yosiaLukumai/FSO/CAD/lasers and laser ho;der assembly.SLDASM

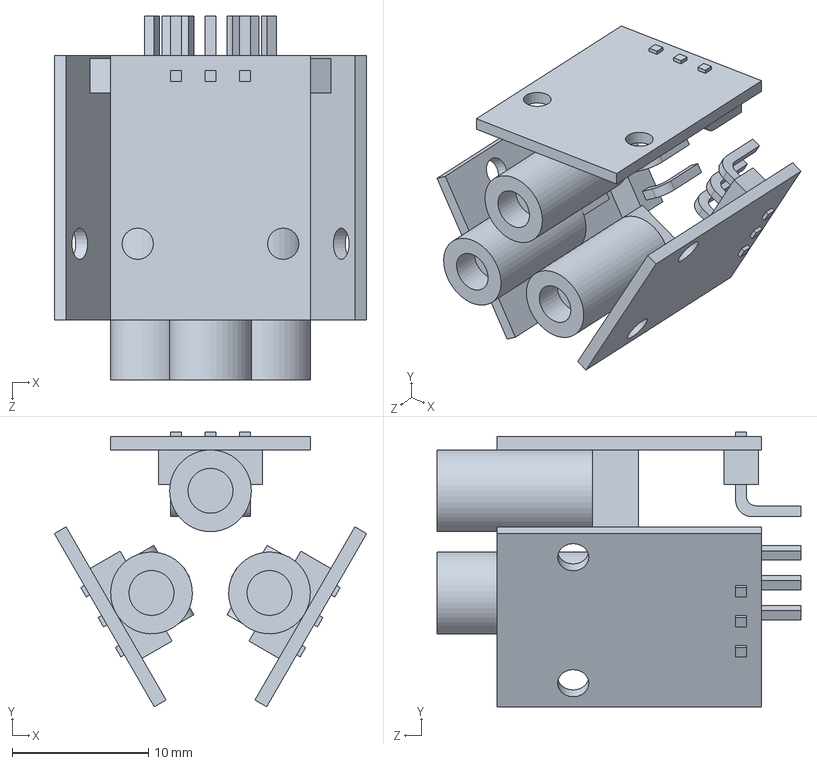
[picture p13: CAD file, 2026-05-01]
CAD/lasers and laser ho;der assembly.SLDASM
22.9 x 20.2 x 26.7 mm
LaserModule x 3
