yosiaLukumai/FSO/CAD/component holder and adjuster.SLDASM

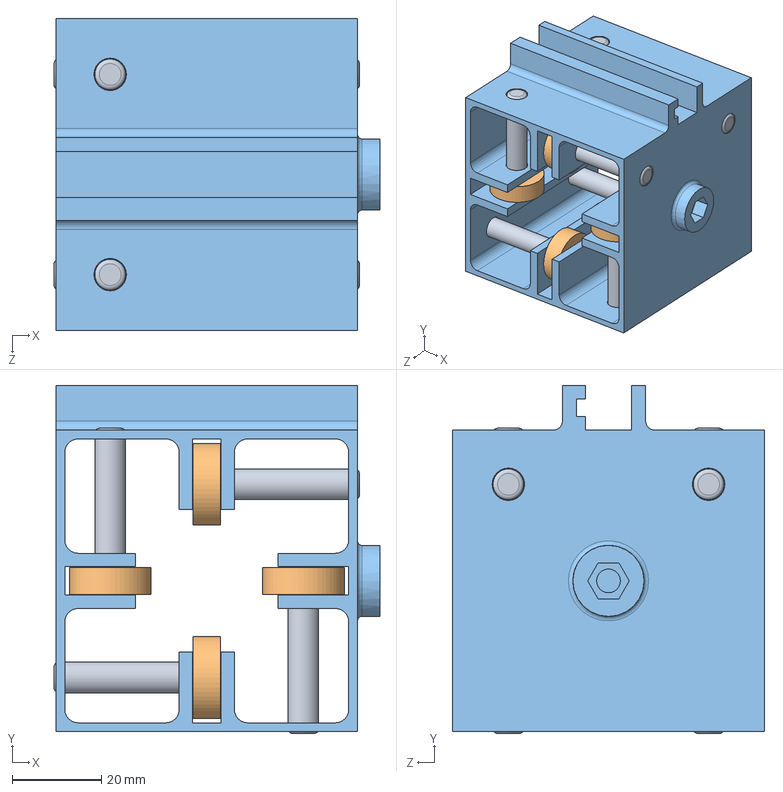
[picture p15: CAD file, 2026-05-01]
CAD/component holder and adjuster.SLDASM
73.2 x 78.2 x 70.0 mm
lens_holder
bearing x 8
bearing_holding_rods x 8
