yosiaLukumai/FSO/CAD/square-pipes-1.snapshot.1/rotation-joint-link.SLDPRT

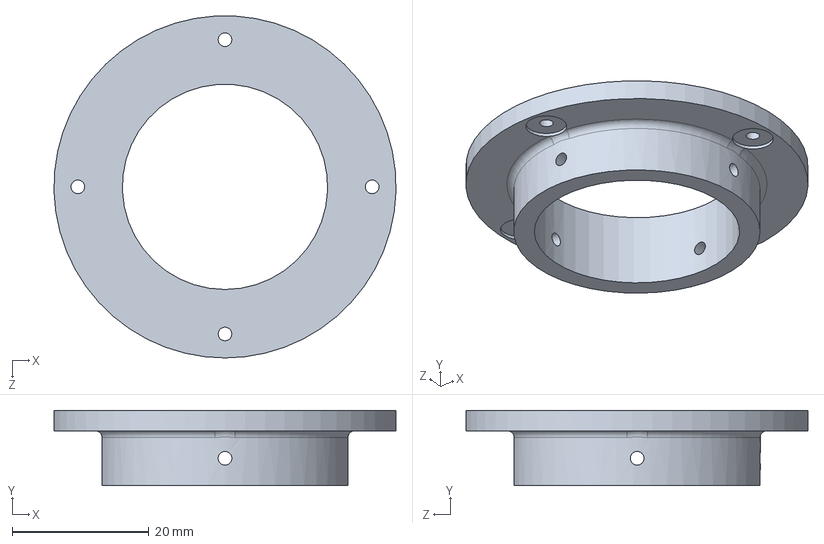
[picture p29: CAD file, 2026-05-01]
CAD/square-pipes-1.snapshot.1/rotation-joint-link.SLDPRT
50.0 x 11.0 x 50.0 mm
