yosiaLukumai/FSO/CAD/adster_concept.SLDPRT

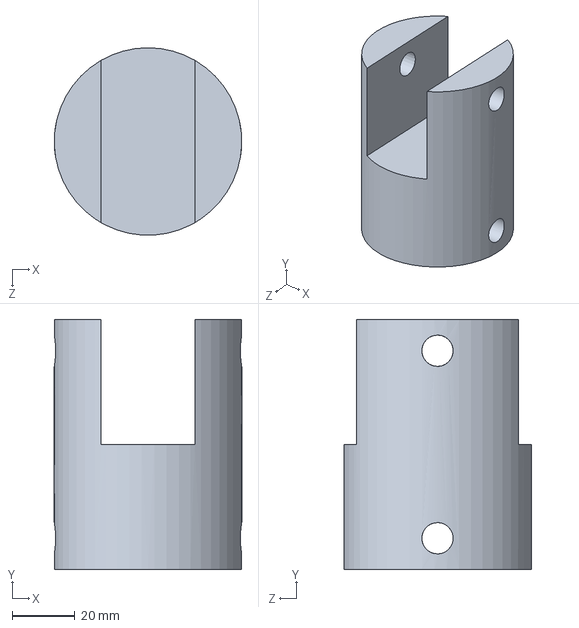
[picture p30: CAD file, 2026-05-01]
CAD/adster_concept.SLDPRT
60.0 x 80.0 x 60.0 mm
