yosiaLukumai/FSO/CAD/square-pipes-1.snapshot.1/rotational joint lock guider.SLDPRT

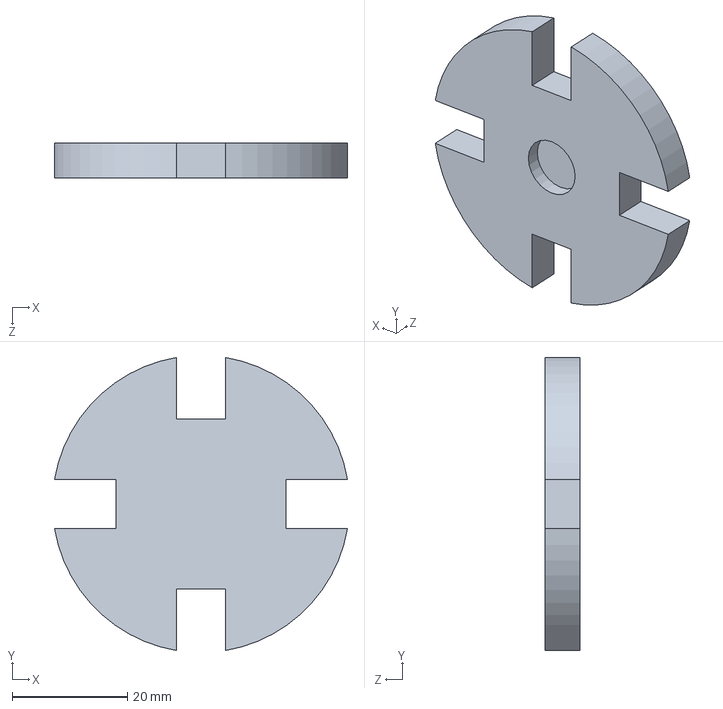
[picture p31: CAD file, 2026-05-01]
CAD/square-pipes-1.snapshot.1/rotational joint lock guider.SLDPRT
50.8 x 50.8 x 6.00 mm
