yosiaLukumai/FSO/CAD/convex22_V2.0.SLDPRT

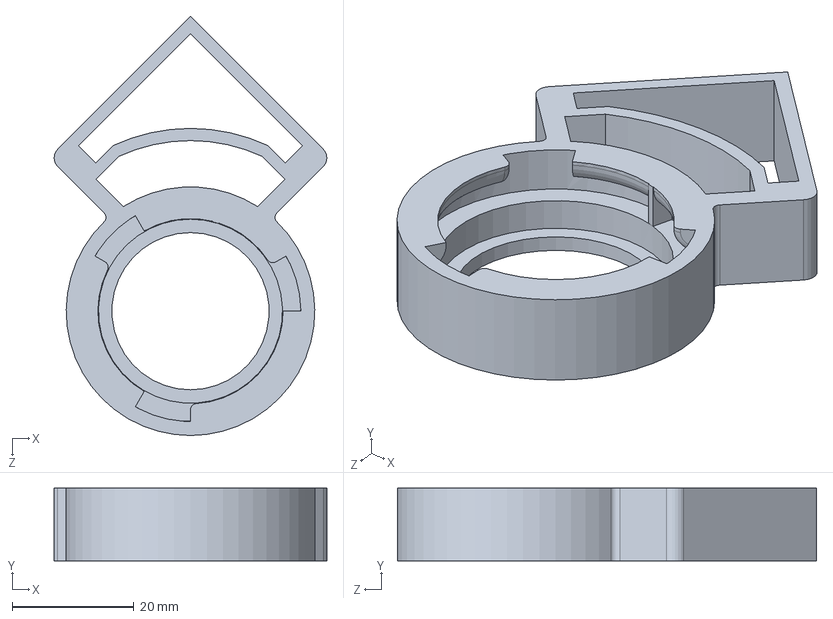
[picture p32: CAD file, 2026-05-01]
CAD/convex22_V2.0.SLDPRT
44.8 x 11.9 x 68.8 mm
