yosiaLukumai/FSO/CAD/square-pipes-1.snapshot.1/pitch lock modified.SLDPRT

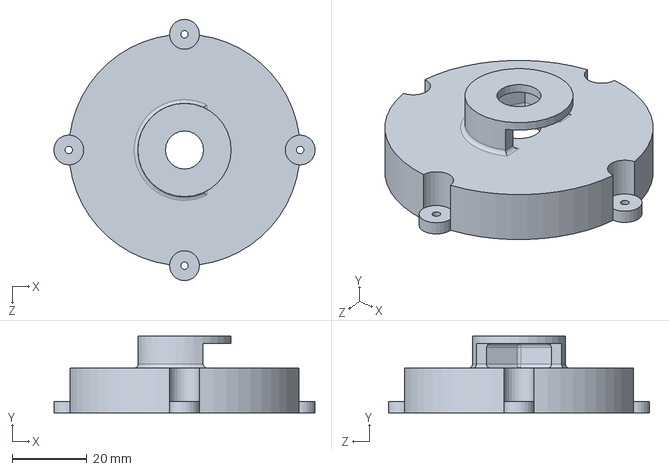
[picture p33: CAD file, 2026-05-01]
CAD/square-pipes-1.snapshot.1/pitch lock modified.SLDPRT
69.9 x 20.5 x 69.9 mm
