yosiaLukumai/FSO/CAD/bearing.SLDPRT

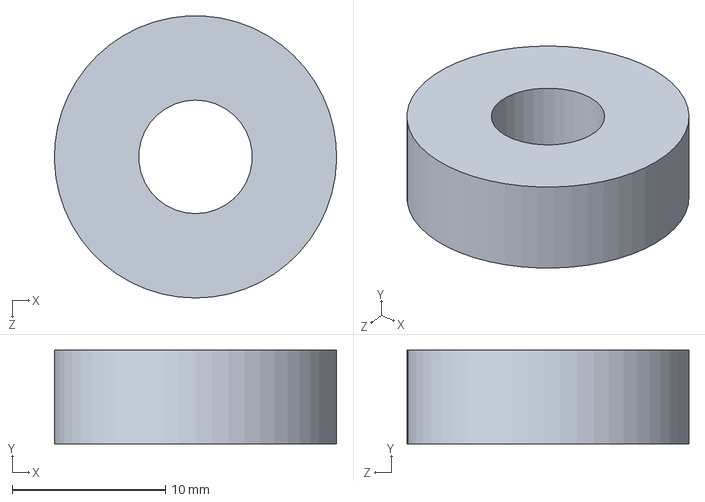
[picture p34: CAD file, 2026-05-01]
CAD/bearing.SLDPRT
18.4 x 6.10 x 18.4 mm
