yosiaLukumai/FSO/CAD/rotatonal joint external lock.SLDPRT

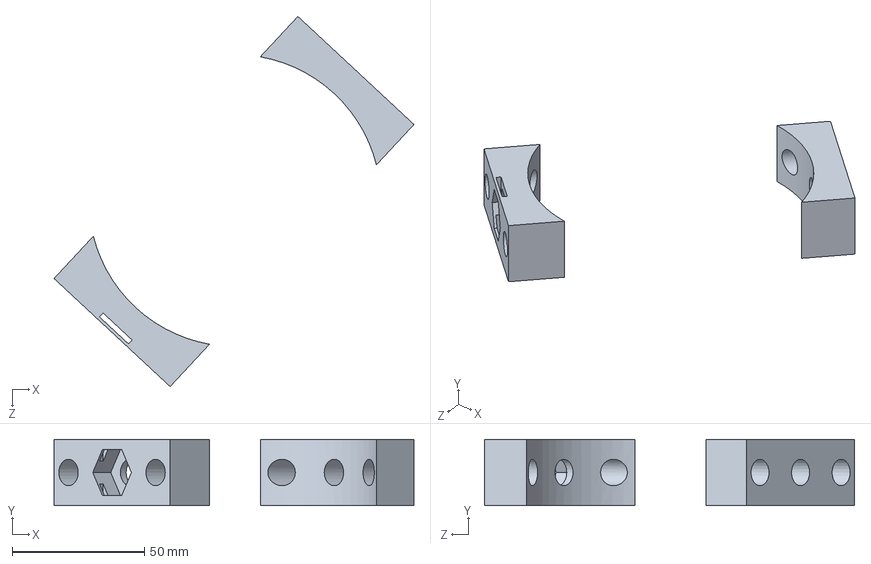
[picture p35: CAD file, 2026-05-01]
CAD/rotatonal joint external lock.SLDPRT
136.2 x 25.0 x 140.0 mm
