yosiaLukumai/FSO/CAD/square-pipes-1.snapshot.1/Slot guider.SLDPRT

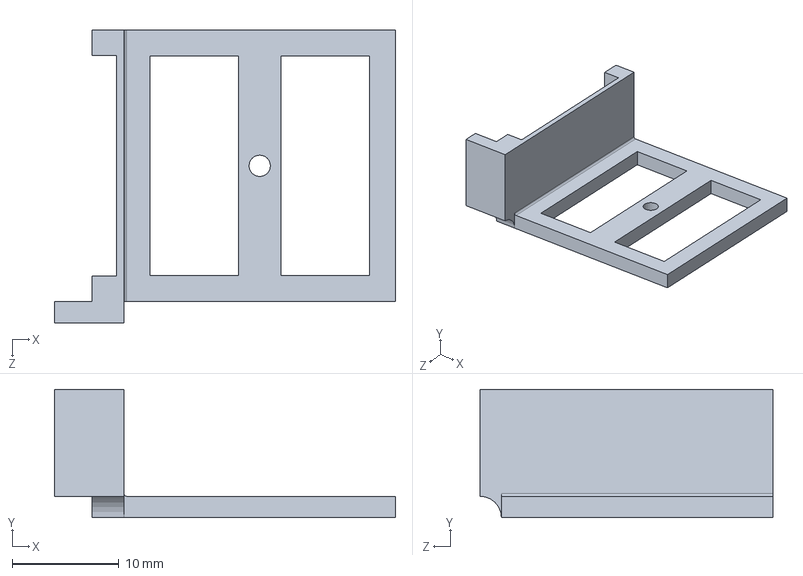
[picture p36: CAD file, 2026-05-01]
CAD/square-pipes-1.snapshot.1/Slot guider.SLDPRT
31.9 x 12.0 x 27.4 mm
