yosiaLukumai/FSO/CAD/square-pipes-1.snapshot.1/single receiver holder.SLDPRT

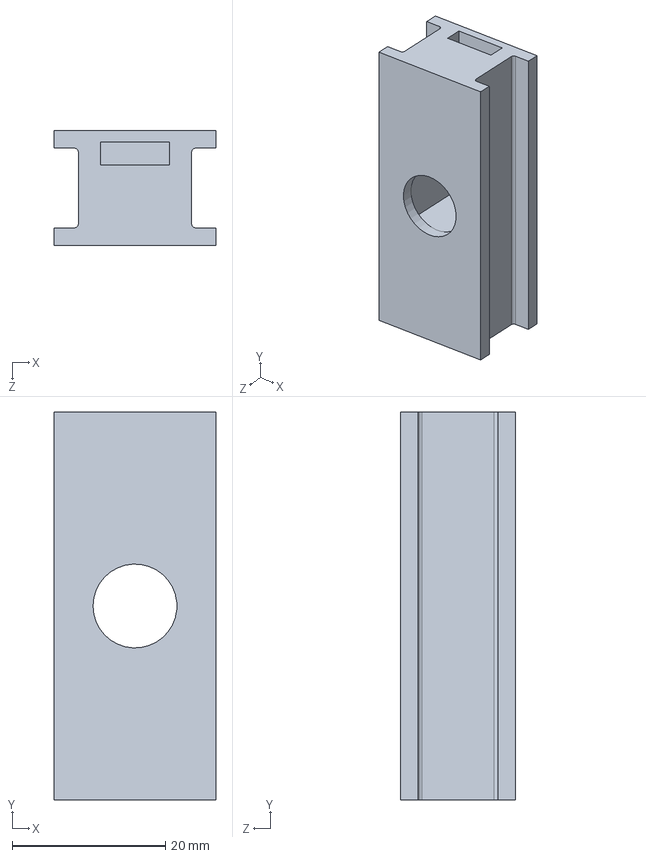
[picture p37: CAD file, 2026-05-01]
CAD/square-pipes-1.snapshot.1/single receiver holder.SLDPRT
21.1 x 50.7 x 15.0 mm
