yosiaLukumai/FSO/CAD/LaserModule.SLDPRT

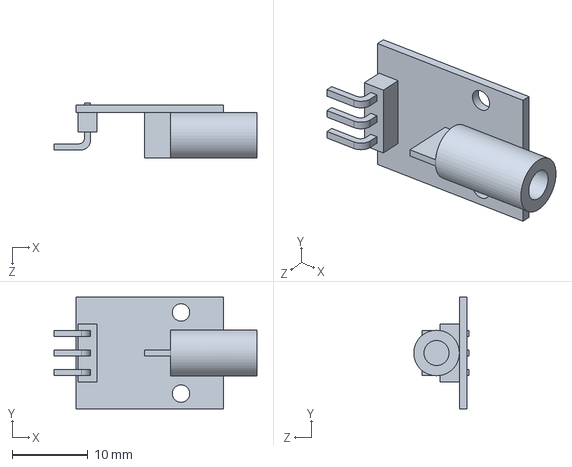
[picture p38: CAD file, 2026-05-01]
CAD/LaserModule.SLDPRT
26.7 x 14.7 x 7.30 mm
