yosiaLukumai/FSO/CAD/square-pipes-1.snapshot.1/side locks.SLDPRT

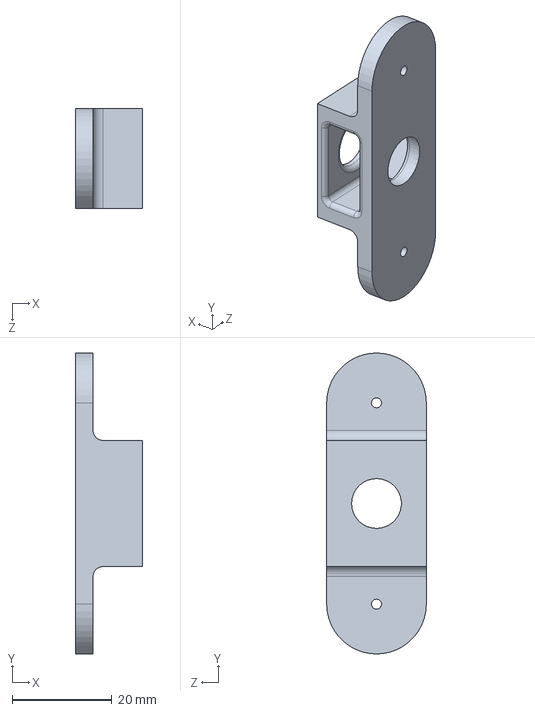
[picture p39: CAD file, 2026-05-01]
CAD/square-pipes-1.snapshot.1/side locks.SLDPRT
13.4 x 60.4 x 20.0 mm
