yosiaLukumai/FSO/CAD/square-pipes-1.snapshot.1/bearing_holding_rods.SLDPRT

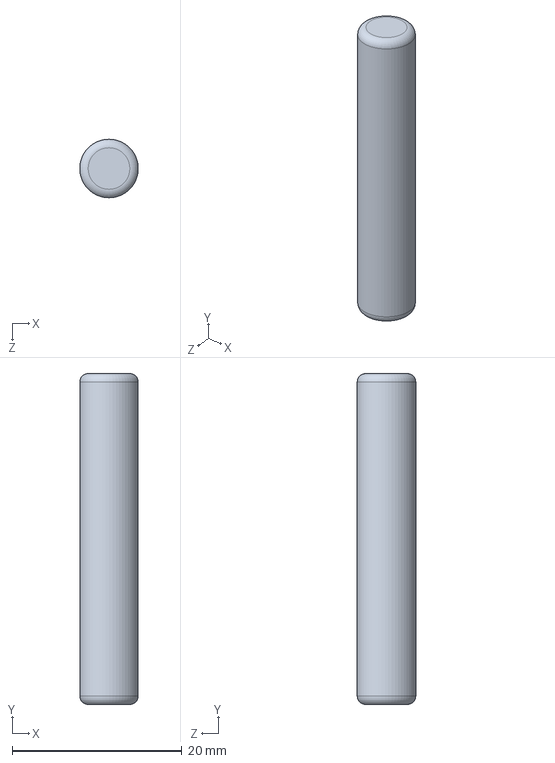
[picture p40: CAD file, 2026-05-01]
CAD/square-pipes-1.snapshot.1/bearing_holding_rods.SLDPRT
6.89 x 39.0 x 6.90 mm
