yosiaLukumai/FSO/CAD/square-pipes-1.snapshot.1/enclosure.SLDPRT

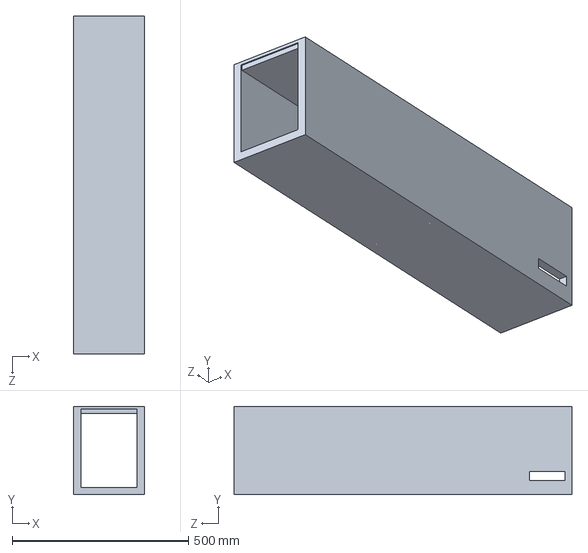
[picture p41: CAD file, 2026-05-01]
CAD/square-pipes-1.snapshot.1/enclosure.SLDPRT
200.4 x 250.0 x 960.0 mm
