yosiaLukumai/FSO/CAD/square-pipes-1.snapshot.1/standing pole.SLDPRT

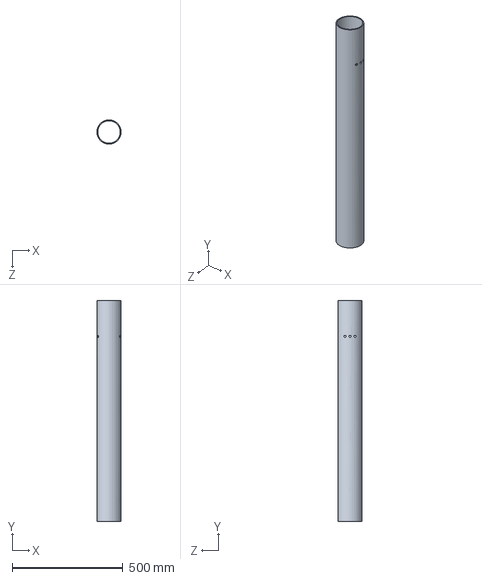
[picture p42: CAD file, 2026-05-01]
CAD/square-pipes-1.snapshot.1/standing pole.SLDPRT
110.0 x 1000.0 x 110.0 mm
