yosiaLukumai/FSO/CAD/pole.SLDPRT

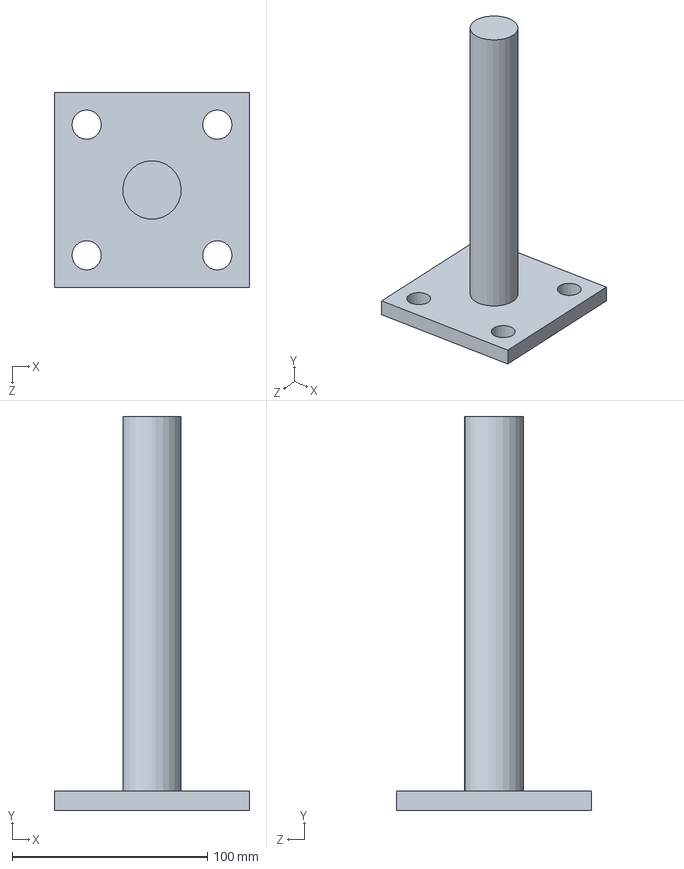
[picture p43: CAD file, 2026-05-01]
CAD/pole.SLDPRT
100.0 x 202.0 x 100.0 mm
