yosiaLukumai/FSO/CAD/square-pipes-1.snapshot.1/square pipe holder.SLDPRT

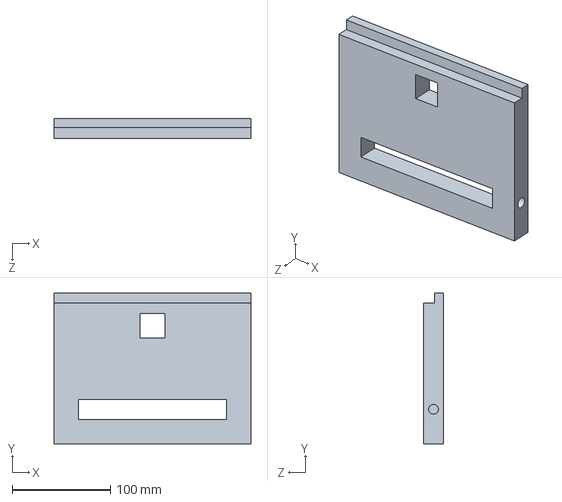
[picture p44: CAD file, 2026-05-01]
CAD/square-pipes-1.snapshot.1/square pipe holder.SLDPRT
200.4 x 153.4 x 20.0 mm
