yosiaLukumai/FSO/CAD/mod2.SLDPRT

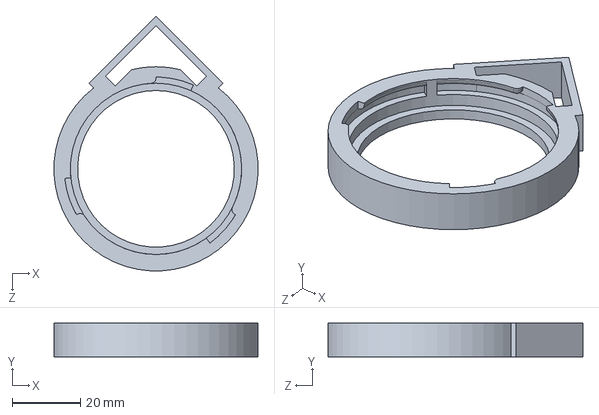
[picture p45: CAD file, 2026-05-01]
CAD/mod2.SLDPRT
59.9 x 9.90 x 74.8 mm
