yosiaLukumai/FSO/CAD/square-pipes-1.snapshot.1/rotation-joint.SLDPRT

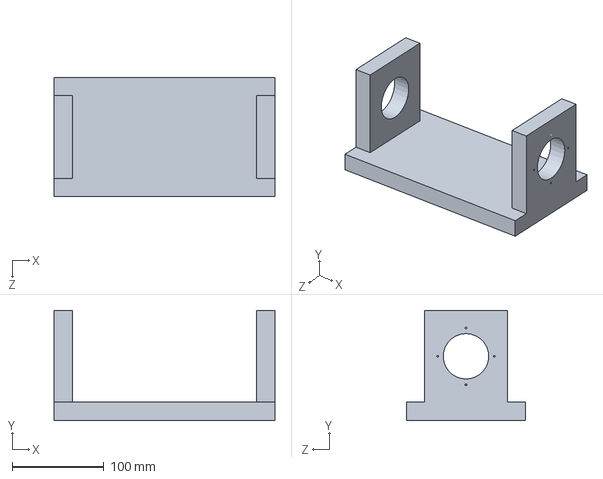
[picture p46: CAD file, 2026-05-01]
CAD/square-pipes-1.snapshot.1/rotation-joint.SLDPRT
241.0 x 120.0 x 130.0 mm
