yosiaLukumai/FSO/CAD/convexSeal1.SLDPRT

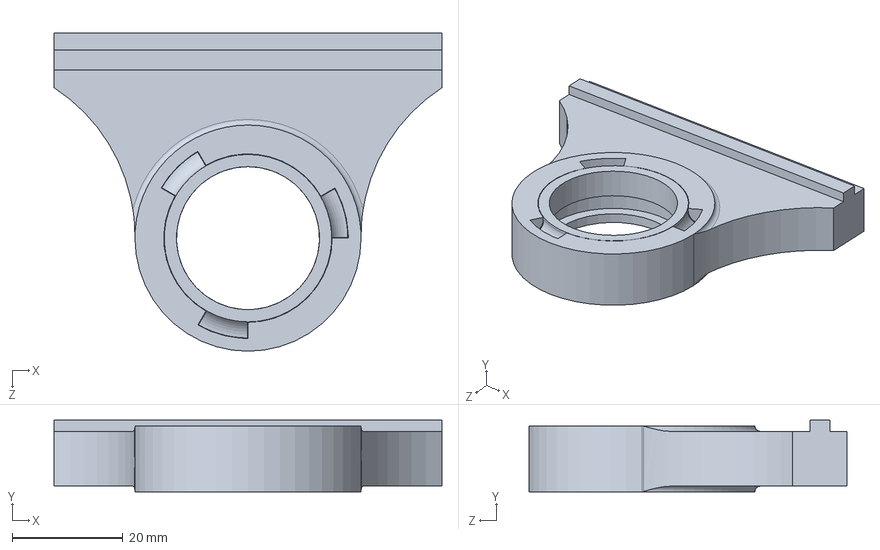
[picture p47: CAD file, 2026-05-01]
CAD/convexSeal1.SLDPRT
70.0 x 12.9 x 57.5 mm
