yosiaLukumai/FSO/CAD/square-pipes-1.snapshot.1/sensor_receiver.SLDPRT

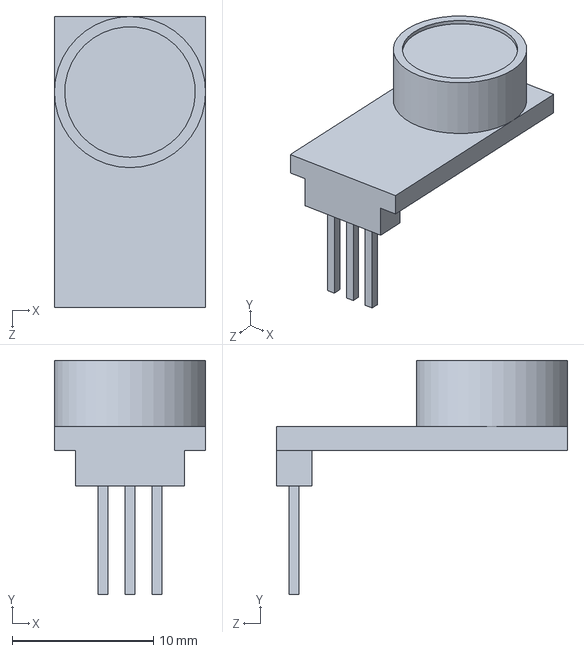
[picture p48: CAD file, 2026-05-01]
CAD/square-pipes-1.snapshot.1/sensor_receiver.SLDPRT
10.7 x 16.6 x 20.6 mm
