yosiaLukumai/FSO/CAD/base.SLDPRT

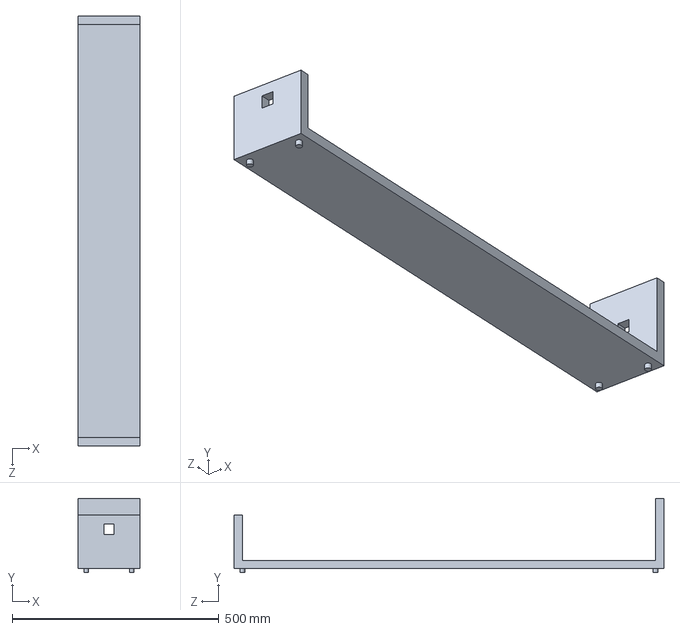
[picture p49: CAD file, 2026-05-01]
CAD/base.SLDPRT
150.0 x 180.0 x 1040.0 mm
