yosiaLukumai/FSO/CAD/square-pipes-1.snapshot.1/dual receiver holder.SLDPRT

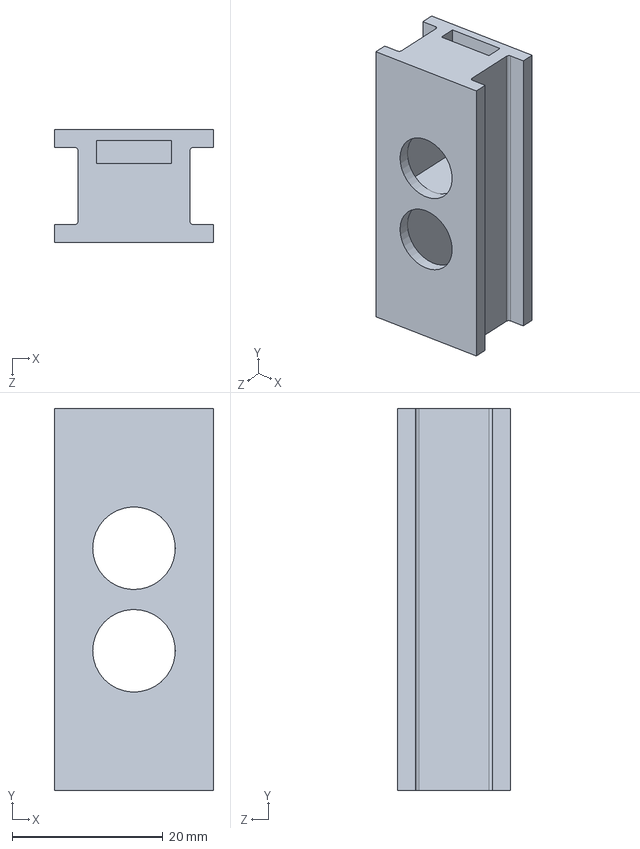
[picture p50: CAD file, 2026-05-01]
CAD/square-pipes-1.snapshot.1/dual receiver holder.SLDPRT
21.1 x 50.7 x 15.0 mm
