yosiaLukumai/FSO/CAD/m10 thread rods.SLDPRT

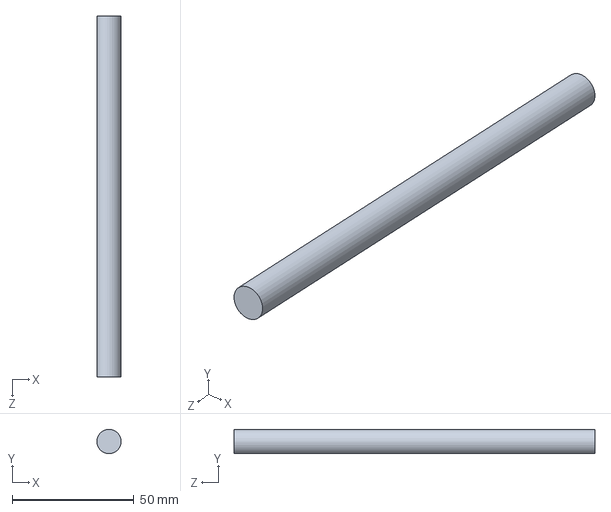
[picture p51: CAD file, 2026-05-01]
CAD/m10 thread rods.SLDPRT
10.0 x 9.99 x 148.5 mm
