yosiaLukumai/FSO/CAD/square-pipes-1.snapshot.1/receiver holder.SLDPRT

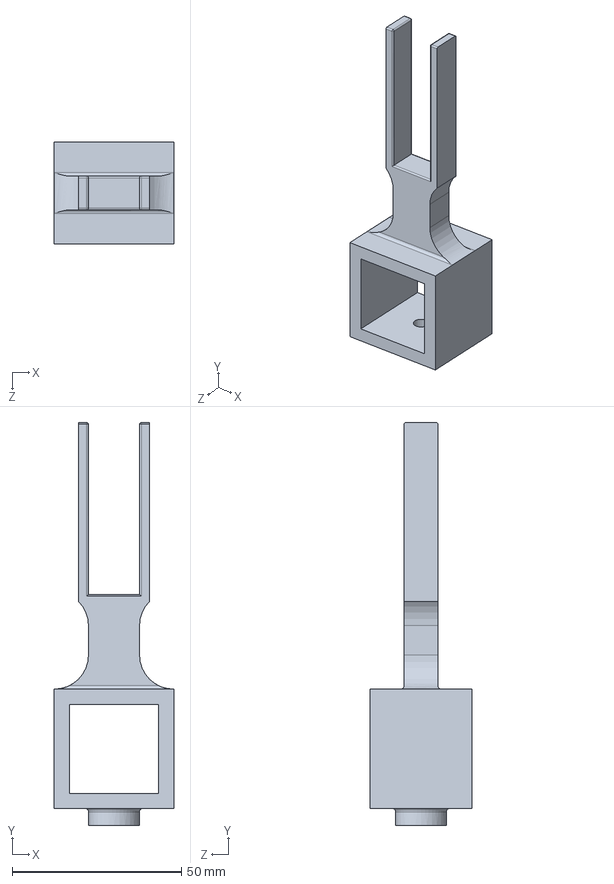
[picture p52: CAD file, 2026-05-01]
CAD/square-pipes-1.snapshot.1/receiver holder.SLDPRT
35.3 x 119.0 x 30.0 mm
