yosiaLukumai/FSO/CAD/laser-module-housing.SLDPRT

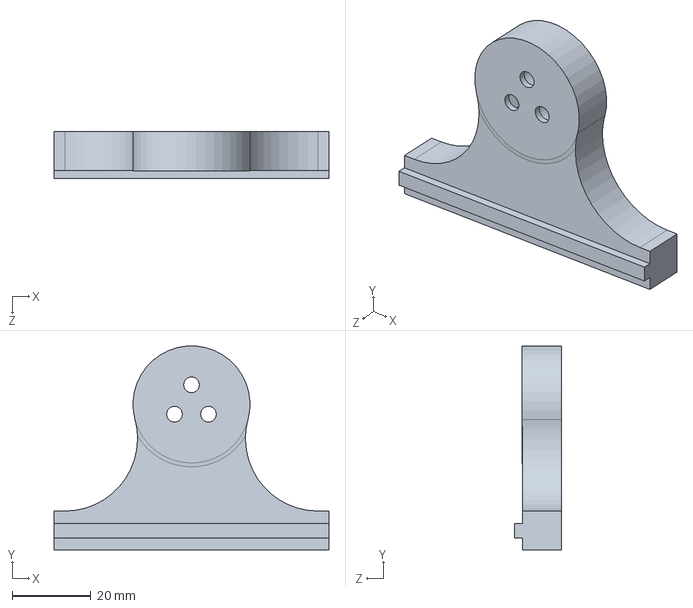
[picture p53: CAD file, 2026-05-01]
CAD/laser-module-housing.SLDPRT
70.0 x 51.9 x 12.0 mm
