yosiaLukumai/FSO/CAD/square-pipes-1.snapshot.1/Door_Side_Locker_Inside.SLDPRT

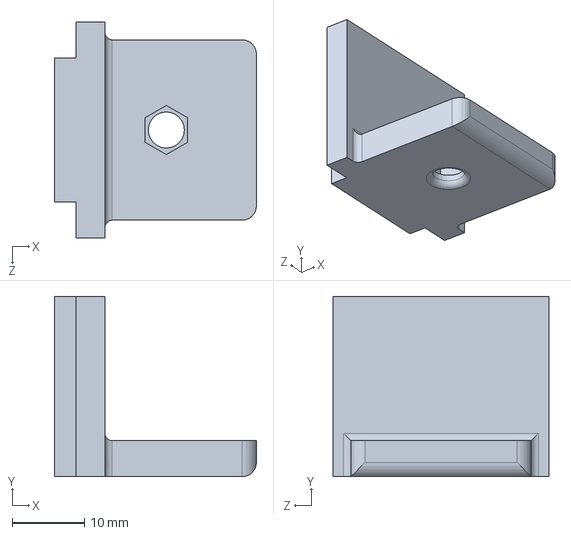
[picture p54: CAD file, 2026-05-01]
CAD/square-pipes-1.snapshot.1/Door_Side_Locker_Inside.SLDPRT
28.0 x 25.0 x 30.0 mm
