yosiaLukumai/FSO/CAD/square-pipes-1.snapshot.1/square pipe to slider connector.SLDPRT

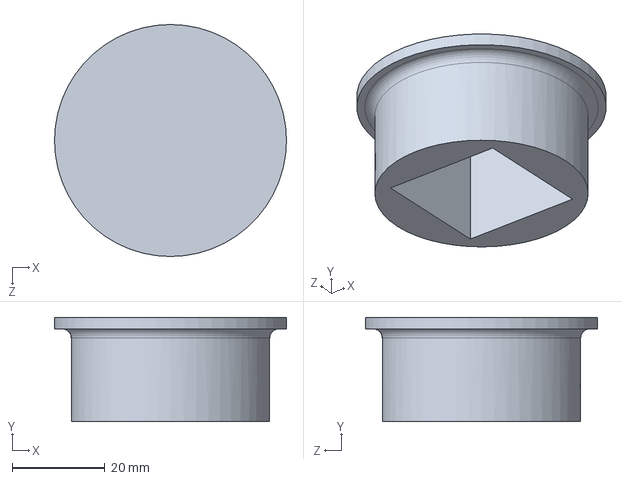
[picture p55: CAD file, 2026-05-01]
CAD/square-pipes-1.snapshot.1/square pipe to slider connector.SLDPRT
50.0 x 22.5 x 50.0 mm
