yosiaLukumai/FSO/CAD/square-pipes-1.snapshot.1/Door_Side_Locker_Outside.SLDPRT

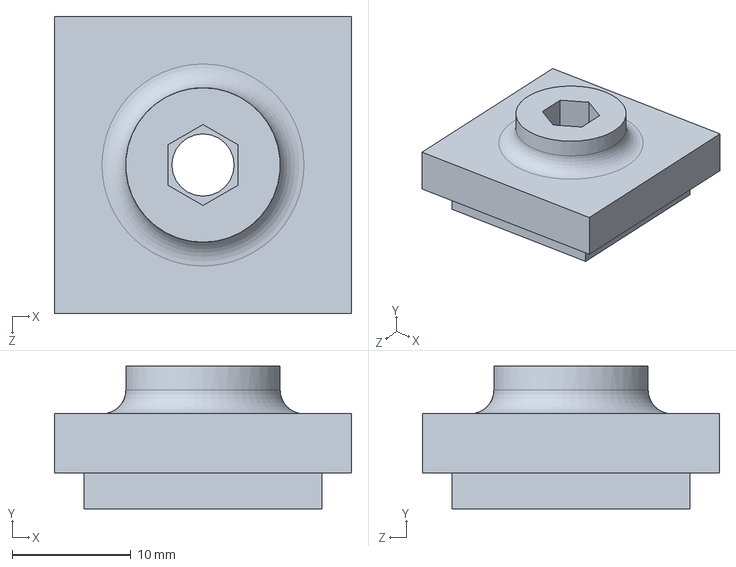
[picture p56: CAD file, 2026-05-01]
CAD/square-pipes-1.snapshot.1/Door_Side_Locker_Outside.SLDPRT
25.0 x 12.0 x 25.0 mm
