yosiaLukumai/FSO/CAD/square-pipes-1.snapshot.1/stoppers.SLDPRT

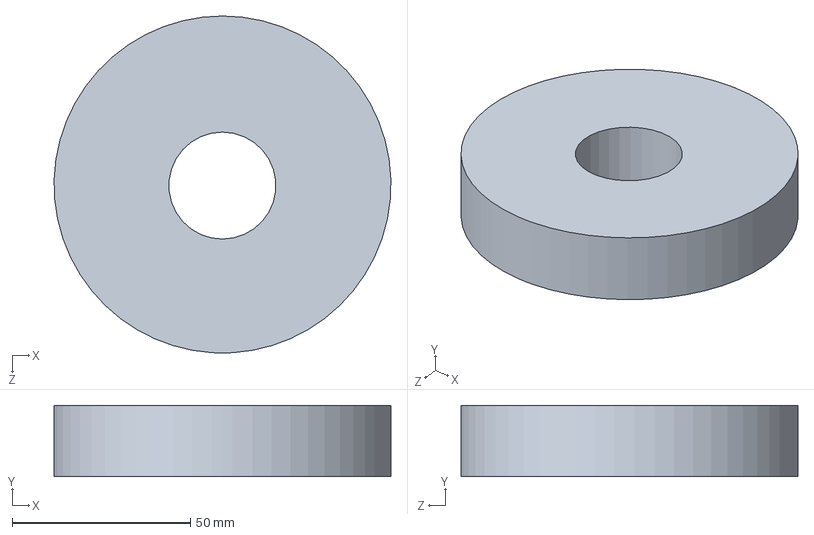
[picture p57: CAD file, 2026-05-01]
CAD/square-pipes-1.snapshot.1/stoppers.SLDPRT
94.5 x 20.0 x 94.5 mm
