yosiaLukumai/FSO/CAD/square-pipes-1.snapshot.1/friction disk.SLDPRT

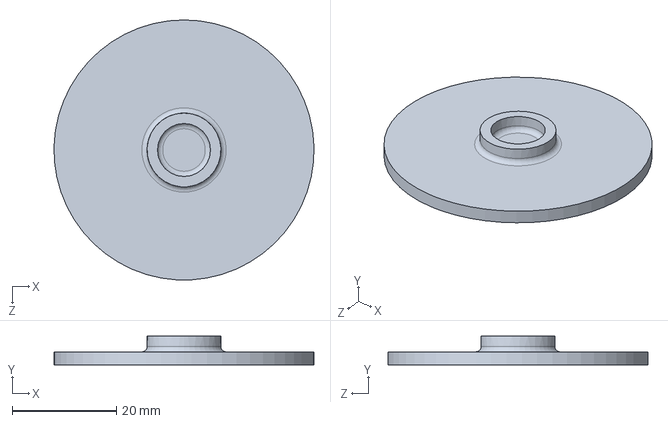
[picture p58: CAD file, 2026-05-01]
CAD/square-pipes-1.snapshot.1/friction disk.SLDPRT
50.0 x 5.50 x 50.0 mm
