yosiaLukumai/FSO/CAD/square-pipes-1.snapshot.1/wood slider nuts holder.SLDPRT

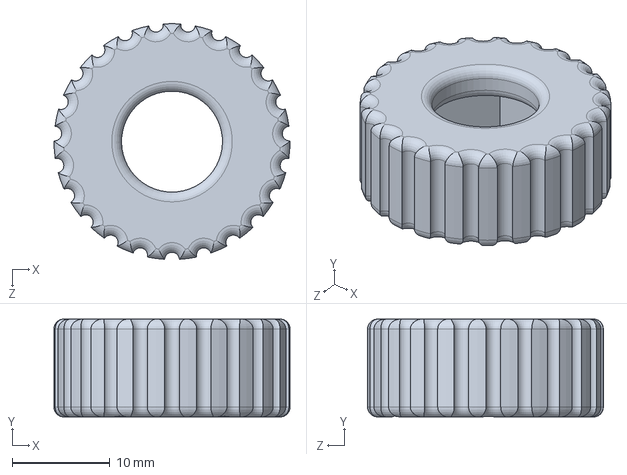
[picture p59: CAD file, 2026-05-01]
CAD/square-pipes-1.snapshot.1/wood slider nuts holder.SLDPRT
24.1 x 10.0 x 24.1 mm
