yosiaLukumai/FSO/CAD/square-pipes-1.snapshot.1/wood slider nuts.SLDPRT

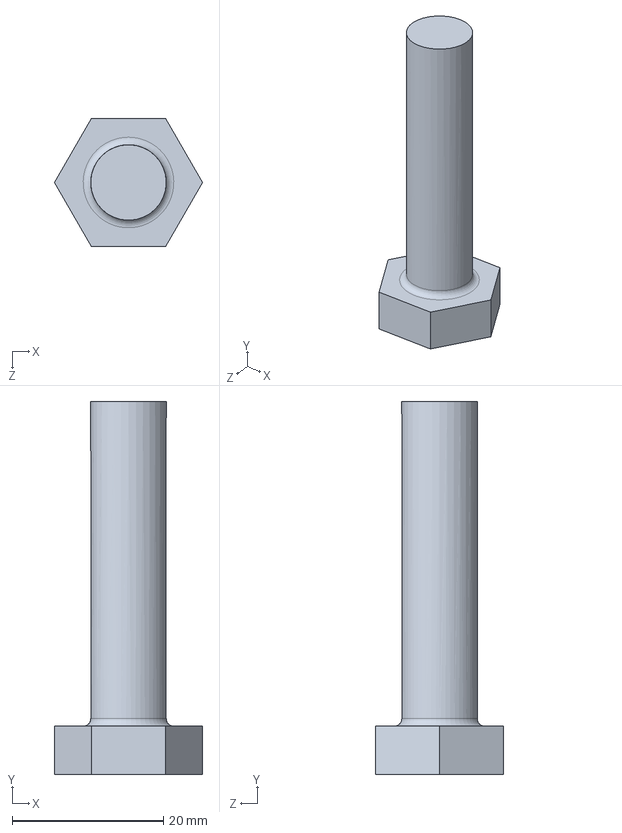
[picture p60: CAD file, 2026-05-01]
CAD/square-pipes-1.snapshot.1/wood slider nuts.SLDPRT
19.6 x 49.4 x 17.0 mm
