yosiaLukumai/FSO/CAD/square-pipes-1.snapshot.1/25mm square pipe.SLDPRT

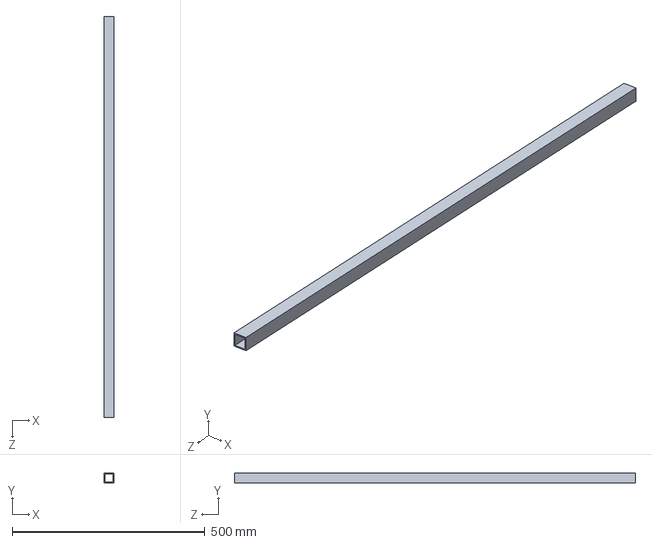
[picture p61: CAD file, 2026-05-01]
CAD/square-pipes-1.snapshot.1/25mm square pipe.SLDPRT
25.0 x 25.0 x 1040.0 mm
