yosiaLukumai/FSO/CAD/square-pipes-1.snapshot.1/adjustable base.SLDPRT

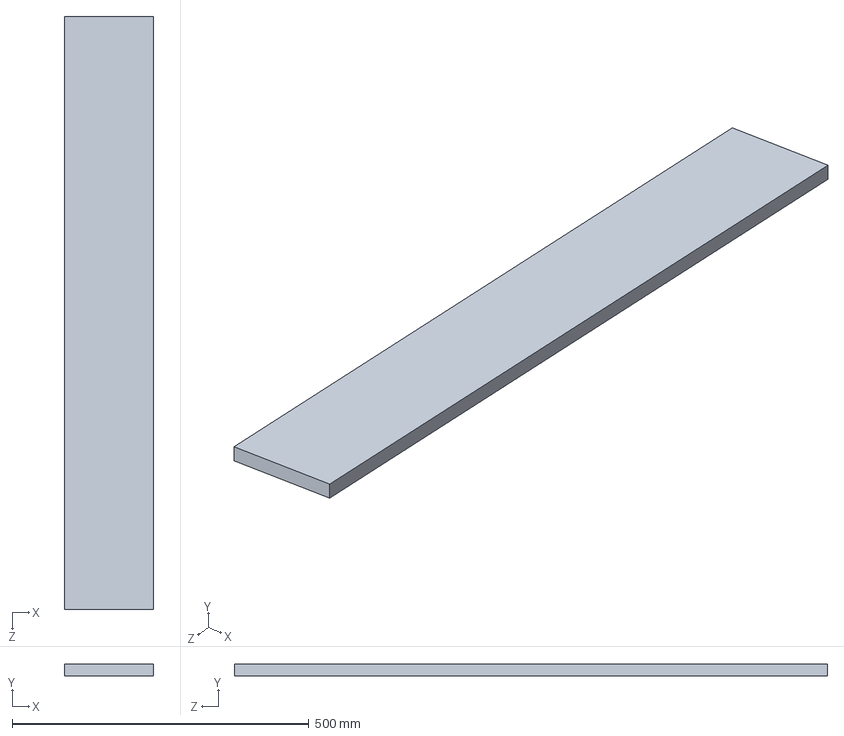
[picture p62: CAD file, 2026-05-01]
CAD/square-pipes-1.snapshot.1/adjustable base.SLDPRT
150.0 x 20.0 x 1000.0 mm
