yosiaLukumai/FSO/CAD/square-pipes-1.snapshot.1/slider-ring.SLDPRT

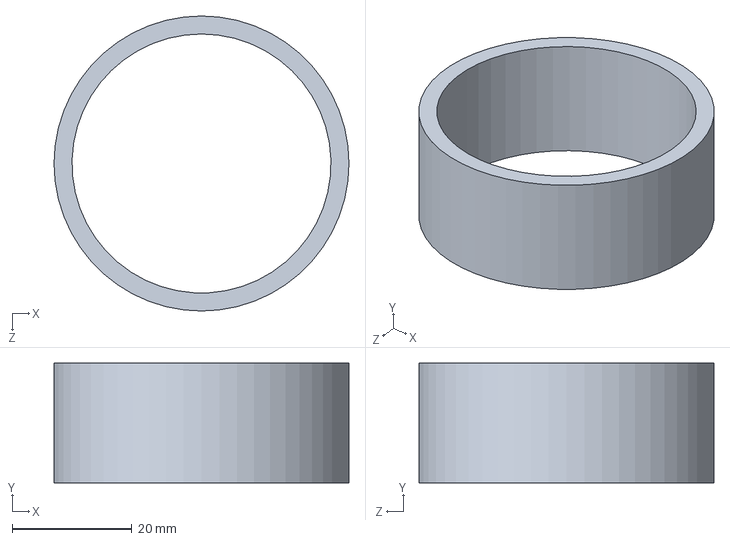
[picture p63: CAD file, 2026-05-01]
CAD/square-pipes-1.snapshot.1/slider-ring.SLDPRT
49.2 x 20.0 x 49.2 mm
