yosiaLukumai/FSO/CAD/square-pipes-1.snapshot.1/Square Pipes 1x1x575x2.3t.SLDPRT

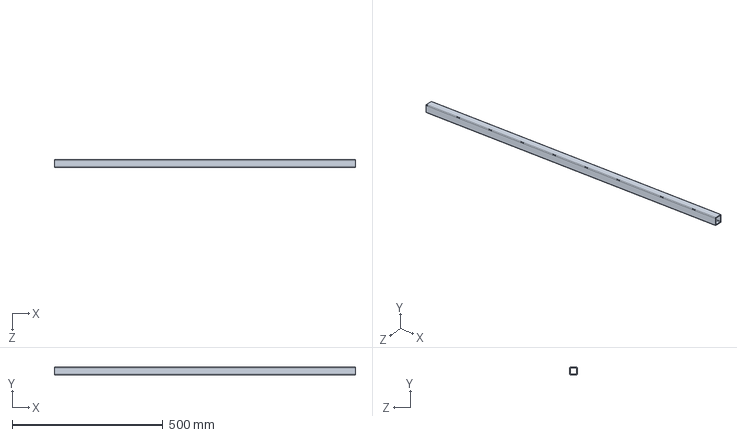
[picture p64: CAD file, 2026-05-01]
CAD/square-pipes-1.snapshot.1/Square Pipes 1x1x575x2.3t.SLDPRT
1000.0 x 25.0 x 25.0 mm
