yosiaLukumai/FSO/results/field_setup.jpg

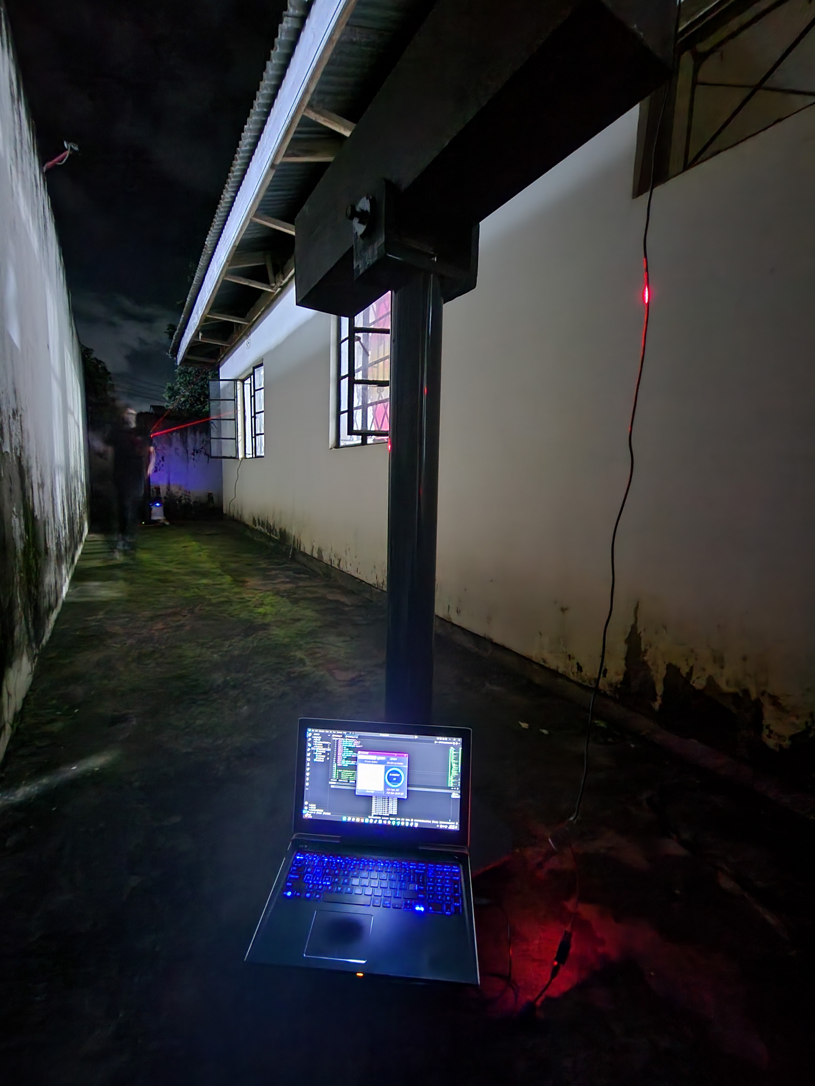
results/field_setup.jpg
