yosiaLukumai/FSO/results/power_metrics.png

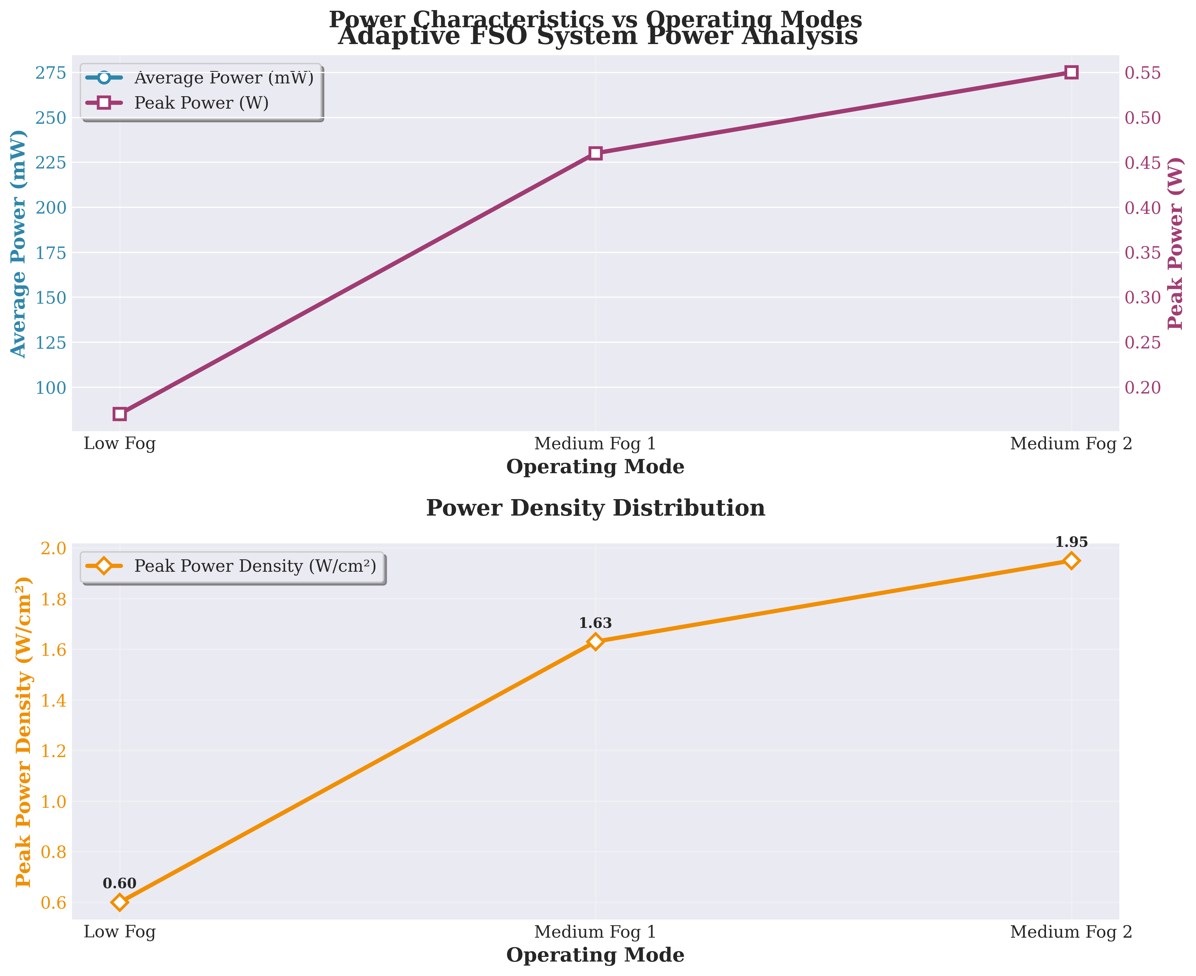
results/power_metrics.png
